Cell1729/AudioAMP/circuit/circuit.kicad_pcb

## KiCad design electronics/wiring-schematic/Wiring_Schematic.kicad_sch

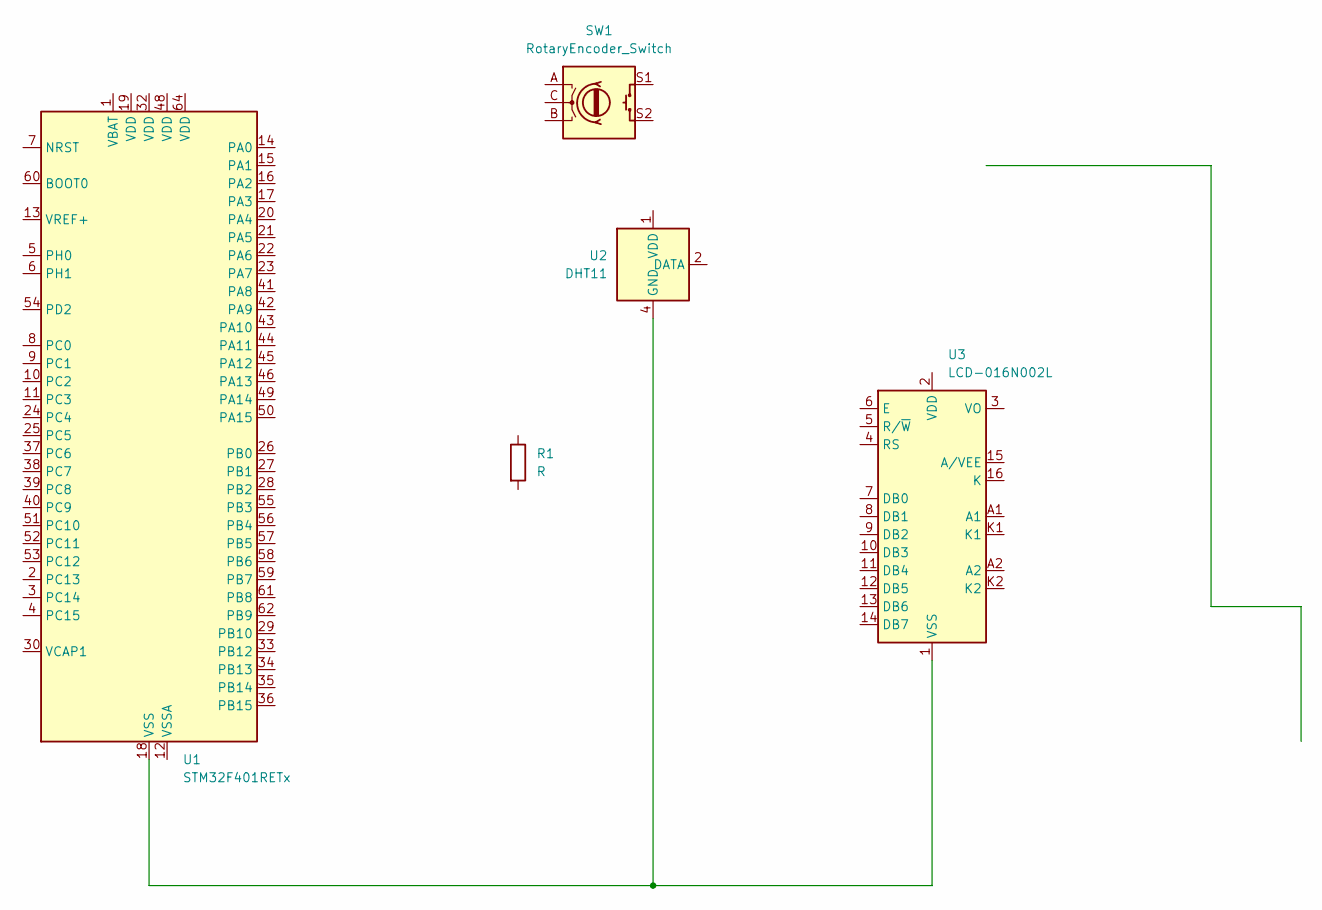
[picture p17: schematic Wiring_Schematic.kicad_sch]

Parts:
R1: R
SW1: RotaryEncoder_Switch
U1: STM32F401RETx; LQFP-64_10x10mm_P0.5mm
U2: DHT11; Aosong_DHT11_5.5x12.0_P2.54mm
U3: LCD-016N002L

Connections:
unnamed: U1.18 (VSS), U1.31 (VSS), U1.47 (VSS), U1.63 (VSS), U2.4 (GND), U3.1 (VSS)
